jpt13653903/Sonar/LTSpice/ResistorLadder.asc

R1: res; 5.6k
R2: res; 3.6k
R3: res; 10R
R4: res; 5.6k
R5: res; 3.6k
R6: res; 10R
R7: res; 5.6k
R8: res; 3.6k
R9: res; 10R
R10: res; 5.6k
R11: res; 3.6k
R12: res; 10R
R13: res; 5.6k
R14: res; 3.6k
R15: res; 10R
R16: res; 5.6k
R17: res; 3.6k
R18: res; 10R
R19: res; 5.6k
R20: res; 3.6k
R21: res; 10R
R22: res; 5.6k
R23: res; 3.6k
R24: res; 10R
R25: res; 5.6k
R26: res; 3.6k
R27: res; 10R
R28: res; 5.6k
R29: res; 3.6k
R30: res; 10R
R31: res; 5.6k
R32: res; 3.6k
R33: res; 10R
R34: res; 5.6k
R35: res; 3.6k
R36: res; 10R
R37: res; 5.6k
R38: res; 3.6k
R39: res; 10R
R40: res; 5.6k
R41: res; 3.6k
R42: res; 10R
R43: res; 5.6k
R44: res; 3.6k
R45: res; 10R
R46: res; 5.6k
R47: res; 3.6k
R48: res; 10R
R49: res; 3.6k
V1: voltage; SINE(0 1 1k); AC 1
V2: voltage; 5V
Named nets: 0, 5V, VIN
.ac dec 100 1m 1G
.tran 10m
