jpt13653903/Sonar/LTSpice/Amplifier.asc

C1: cap; 100n
R1: res; 1k
R2: res; 100k
U1: opamp2; AD8534
V1: voltage; 5V
V2: voltage; SINE(2.5 1m 10k); AC 1
Named nets: 0, 5V, Vout, Vin
.include ad8534.cir
.ac dec 100 1m 1G
.tran 1m
