jpt13653903/Sonar/LTSpice/Speaker Driver.asc

C1: cap; 220n
C2: cap; 220n
C3: cap; 100p
C4: cap; 100p
C5: cap; 2n2
C6: cap; 2n2
R1: res; 40k
R2: res; 40k
R3: res; 12k
R4: res; 12k
R5: res; 1k
R6: res; 1k
U1: AD8139
V1: voltage; 2.5V
V2: voltage; 5V
V3: voltage; SINE(1.65 1.5 1k); AC 1
Named nets: 0, 5V, VCOM, Vout, Vout_n, vin
.ac dec 100 1m 1G
.tran 10m
